kotbehemot53/universal-nixie-display/firmware/nixie-controller/doc/nixie_board_schematic.png

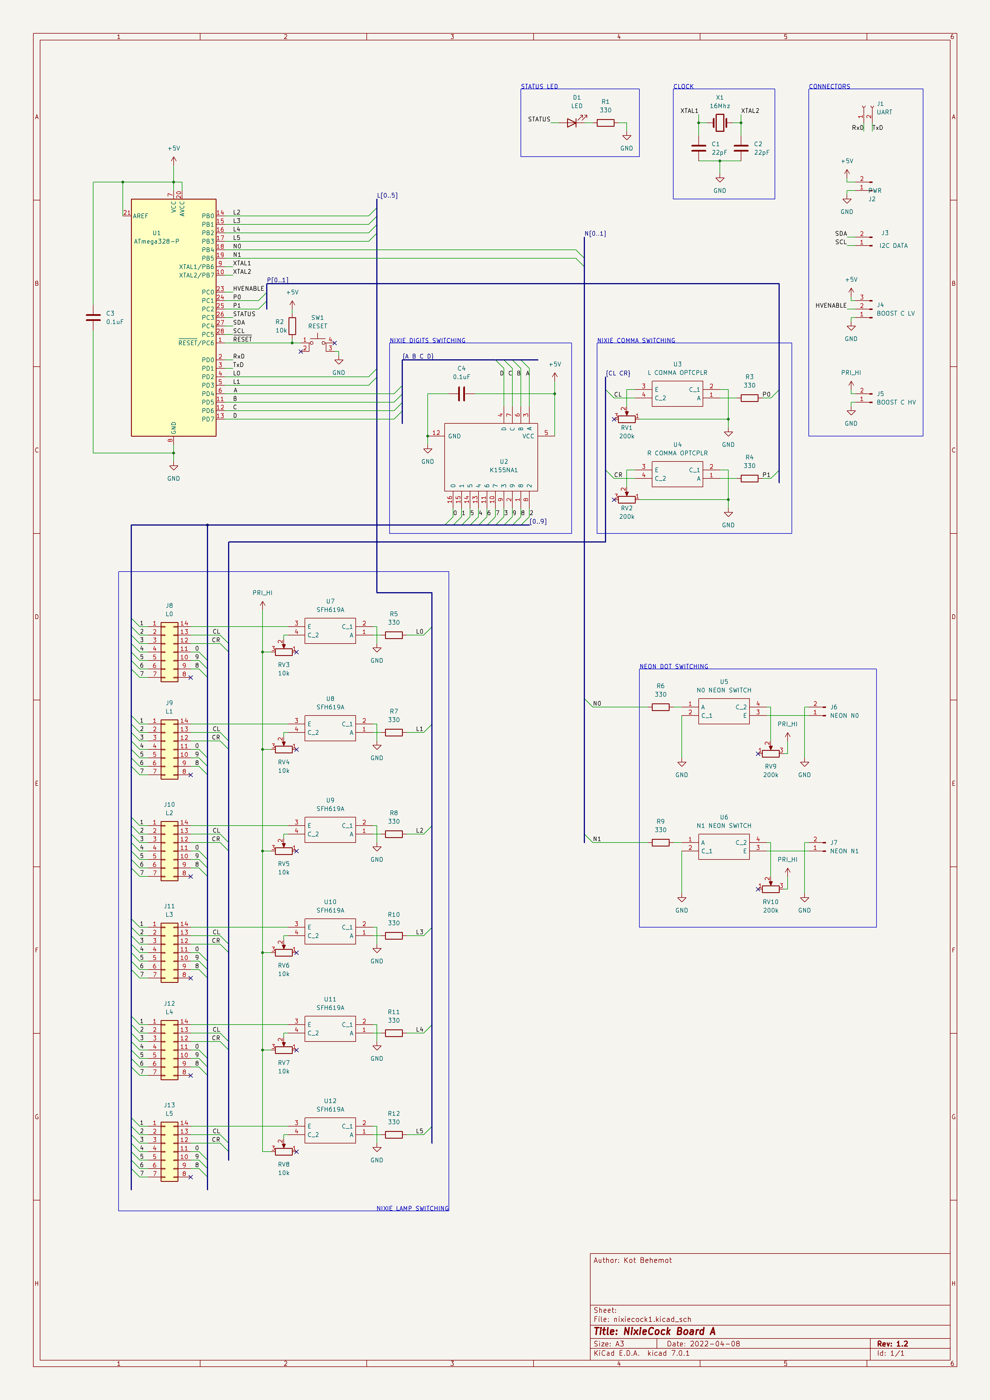
firmware/nixie-controller/doc/nixie_board_schematic.png
