kotbehemot53/universal-nixie-display/hardware/vfd-board/images/vfd-board-3d-front.jpg

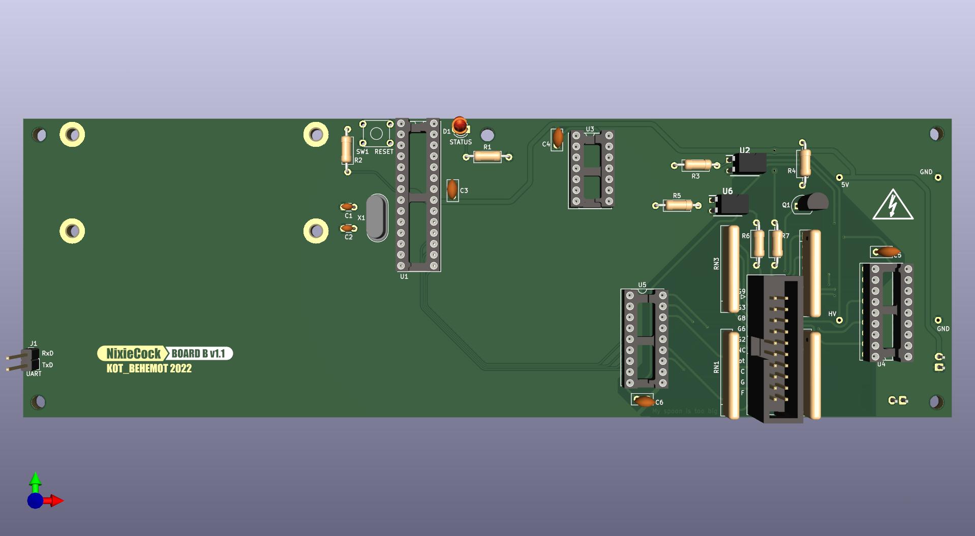
hardware/vfd-board/images/vfd-board-3d-front.jpg
